RecunchoMaker/adefesio/src/control.h

/**
 * @file robot.h
 *
 * @brief Cabecera de robot.cpp
 */

#ifndef __CONTROL_H
#define __CONTROL_H

void control_continua();
void control_espera();
void control_avance();
void control_parada();
void control_giro();
void control_espera_senal();

#endif /* ifndef _CONTROL_H

*/
