RecunchoMaker/adefesio/src/laberinto.cpp

/**
 * @file laberinto.cpp
 *
 * @brief Almacenamiento y tratamiento del laberinto
 *
 * El laberinto se guarda en un array plano de filas x columnas.
 *
 */
#include <Arduino.h>
#include <laberinto.h>
#include <leds.h>
#include <robot.h>
#include <log.h>
#include <camino.h>
#include <flood.h>

//@{
/**
 * @name variables que almacenan el numero de filas y columnas del laberinto actual
 */

volatile int8_t num_filas = LABERINTO_FILAS;       ///< numero de filas
volatile int8_t num_columnas = LABERINTO_COLUMNAS; ///< numero de columnas
//@}

/**
 * @brief Estructura que representa una única casilla en el laberinto
 *
 * - paredN: Es 1 si en la celda se detectó una pared al Norte
 * - paredO: Es 1 si en la celda se detecó una pared al Oeste
 * - visitada: Es 1 si la celda ha sido visitada en la exploración
 * - paso: Guarda el paso correspondiente en el caso de que la celda pertenezca a un camino
 * - flood: distancia (cartesiana) hacia la solución del laberinto, teniendo en cuenta las paredes 
 *   detectadas hasta el momento
 */
typedef struct {
    volatile char paredN : 1;
    volatile char paredO : 1;
    volatile char visitada: 1;
    volatile tipo_paso paso: 2;
    volatile uint8_t flood;
} tipo_celda;

/// Array que contiene todas las celdas del laberinto
volatile tipo_celda celda[MAX_FILAS * MAX_COLUMNAS];




void laberinto_init() {

    laberinto_inicializa_valores();
}

void laberinto_inicializa_valores() {
    int idx = 0;
    for (idx = 0; idx < num_columnas * num_filas; idx++) {
        celda[idx].paredN = idx < num_columnas;
        celda[idx].paredO = idx % num_columnas == 0;
        celda[idx].visitada = 0;
    }

    /*
    celda[17].paredO = 1;
    celda[13].paredO = 1;
    celda[5].paredN = 1;
    celda[8].paredN = 1;
    */

    // Anadir fila dummy
    if (num_filas < MAX_FILAS) {
        celda[num_filas*num_columnas].paredO = 1;
        for (idx = 0; idx < num_columnas; idx++) {
            celda[idx + num_filas*num_columnas].paredN = 1;
        }
    }
}

void laberinto_set_visitada(uint8_t casilla) {
    celda[casilla].visitada = true;
}

char laberinto_get_visitada(uint8_t casilla) {
    return celda[casilla].visitada;
}

void laberinto_set_paso(uint8_t casilla, tipo_paso paso) {
    celda[casilla].paso = paso;
}


tipo_paso laberinto_get_paso(uint8_t casilla) {
    return celda[casilla].paso;
}


bool laberinto_hay_pared_derecha(uint8_t casilla) {
    switch (robot_get_orientacion()) {
        case NORTE: return celda[(uint8_t) (casilla + incremento[ESTE])].paredO;
                    break;
        case ESTE:  return celda[(uint8_t) (casilla + incremento[SUR])].paredN;
                    break;
        case SUR:   return celda[casilla].paredO;
                    break;
        default:    return celda[casilla].paredN;
                    break;
    }
}

bool laberinto_hay_pared_izquierda(uint8_t casilla) {
    switch (robot_get_orientacion()) {
        case NORTE: return celda[casilla].paredO;
                    break;
        case ESTE:  return celda[casilla].paredN;
                    break;
        case SUR:   return celda[(uint8_t) (casilla + incremento[ESTE])].paredO;
                    break;
        default:    return celda[(uint8_t) (casilla + incremento[SUR])].paredN;
                    break;
    }
}
    
bool laberinto_hay_pared_frontal(uint8_t casilla) {
    switch (robot_get_orientacion()) {
        case NORTE: return celda[casilla].paredN;
                    break;
        case ESTE:  return celda[(uint8_t) (casilla + incremento[ESTE])].paredO;
                    break;
        case SUR:   return celda[(uint8_t) (casilla + incremento[SUR])].paredN;
                    break;
        default:    return celda[casilla].paredO;
                    break;
    }
}
    
int8_t laberinto_get_filas() {
    return num_filas;
}
    
int8_t laberinto_get_columnas() {
    return num_columnas;
}


void laberinto_set_paredes_laterales(uint8_t casilla, bool izq, bool der) {
    switch (robot_get_orientacion()) {
        case NORTE: celda[casilla].paredO = izq;
                    celda[(uint8_t) (casilla+incremento[ESTE])].paredO = der;
                    break;
        case ESTE: celda[casilla].paredN = izq;
                    celda[(uint8_t) (casilla+incremento[SUR])].paredN = der;
                    break;
        case SUR:   celda[casilla].paredO = der;
                    celda[(uint8_t) (casilla+incremento[ESTE])].paredO = izq;
                    break;
        case OESTE: celda[casilla].paredN = der;
                    celda[(uint8_t) (casilla+incremento[SUR])].paredN = izq;
                    break;
    }
#ifdef MOCK
    Serial.print(F("setParedLateral "));
    Serial.print(casilla);
    Serial.print(F(" "));
    Serial.print(robot_get_orientacion());
    Serial.print(F(" "));
    Serial.print(izq);
    Serial.print(F(" "));
    Serial.println(der);
#endif
}

void laberinto_set_pared_frontal(uint8_t casilla, bool frontal) {
    switch(robot_get_orientacion()) {
        case NORTE: celda[casilla].paredN = frontal;
                    break;
        case ESTE:  celda[(uint8_t) (casilla + incremento[ESTE])].paredO = frontal;
                    break;
        case SUR:   celda[(uint8_t) (casilla + incremento[SUR])].paredN = frontal;
                    break;
        case OESTE: celda[casilla].paredO = frontal;
                    break;
    }
#ifdef MOCK
    Serial.print(F("setParedFrontal "));
    Serial.print(casilla);
    Serial.print(F(" "));
    Serial.print(robot_get_orientacion());
    Serial.print(F(" "));
    Serial.println(frontal);
#endif
}


/**
 * @brief Envia al puerto serie una representación gráfica del laberinto
 */
void laberinto_print() {

    return ;
#ifndef MOCK
    uint16_t idx = 0;
    uint8_t tipo_linea = 0;

    while (idx < laberinto_get_filas() * laberinto_get_columnas()) {

        switch (tipo_linea) {
        case 0: 
            Serial.print(celda[idx].paredN ? "+-----" : "+     ");
            if (idx % num_columnas == num_columnas - 1)
                Serial.print("+\n");
            break;
        case 1:
            Serial.print(celda[idx].paredO ? "|" : " ");
            Serial.print(celda[idx].visitada ? "." : " ");
            if (flood_get_distancia(idx)< 100) Serial.print(" ");
            if (flood_get_distancia(idx)< 10) Serial.print(" ");
            Serial.print(flood_get_distancia(idx));
            Serial.print(" ");
            if (idx % num_columnas == num_columnas - 1)
                Serial.print("|\n");
            break;
        case 2:
            Serial.print(celda[idx].paredO ? "|" : " ");
            if (celda[idx].paso == PASO_RECTO)
                Serial.print("r");
            else if (celda[idx].paso == PASO_DER)
                Serial.print("d");
            else if (celda[idx].paso == PASO_IZQ)
                Serial.print("i");
            else if (celda[idx].paso == PASO_STOP)
                Serial.print("x");

            if (idx == robot_get_casilla()) {
                Serial.print("  ");
                switch(robot_get_orientacion()) {
                    case NORTE: Serial.print("A"); break;
                    case ESTE:  Serial.print(">"); break;
                    case OESTE: Serial.print("<"); break;
                    case SUR:   Serial.print("V"); break;
                }
                Serial.print(" ");
            } else {
                //Serial.print("    ");
                if (idx< 100) Serial.print(" ");
                if (idx< 10) Serial.print(" ");
                Serial.print(idx);
                Serial.print(" ");
            }

            if (idx % num_columnas == num_columnas - 1)
                Serial.print("|\n");
            break;
        }

        idx++;

        if (idx % num_columnas == 0) {
            tipo_linea++;
            if (tipo_linea <= 2) {
                // repito las casillas con otra linea
                idx -= num_columnas;
            } else {
                tipo_linea = 0;
            }
        }
    }
    // Ultima linea
    for (idx = 0; idx < num_columnas; idx++)
        Serial.print("+-----");
    Serial.print(F("+\n"));
#endif
}


bool laberinto_hay_pared_norte(uint8_t casilla) {
    return celda[casilla].paredN;
}

bool laberinto_hay_pared_sur(uint8_t casilla) {
    return celda[(uint8_t) (casilla + incremento[SUR])].paredN;
}

bool laberinto_hay_pared_este(uint8_t casilla) {
    return celda[(uint8_t) (casilla + incremento[ESTE])].paredO;
}

bool laberinto_hay_pared_oeste(uint8_t casilla) {
    return celda[casilla].paredO;
}
