RecunchoMaker/adefesio/src/camino.h

/**
 * @file camino.h
 *
 * @brief Cabecera de camino.cpp
 */

#ifndef __CAMINO_H
#define __CAMINO_H

#include <Arduino.h>

enum tipo_paso {PASO_RECTO, PASO_DER, PASO_IZQ, PASO_STOP};

void camino_init();
void camino_init(uint8_t origen, uint8_t orientacion);
void camino_empieza();
uint8_t camino_get_casilla_origen();
uint8_t camino_get_casilla_actual();
uint8_t camino_get_orientacion_origen();
uint8_t camino_get_ultima_casilla();
bool camino_es_fin();
bool camino_get_todas_visitadas();
void camino_siguiente_casilla();
void camino_anadir_paso(tipo_paso paso);
void camino_anadir_paso_recto();
void camino_anadir_paso_izq();
void camino_anadir_paso_der();
bool camino_recalcula();

#endif /* ifndef _CAMINO_H

 */
