RecunchoMaker/adefesio/src/comando.h

/**
 * @file comando.h
 *
 * @brief Cabecera de comando.cpp
 */

#ifndef __COMANDO_H
#define __COMANDO_H

void comando_init();
void comando_prompt();
void comando_lee_serial();
void comando_set_go();
bool comando_get_go();

#endif /* ifndef _COMANDO_H

 */
